Makerfabs/MaTouch-ESP32-S3-7.5-Eink-AI-Mic-Array/image/001.bmp

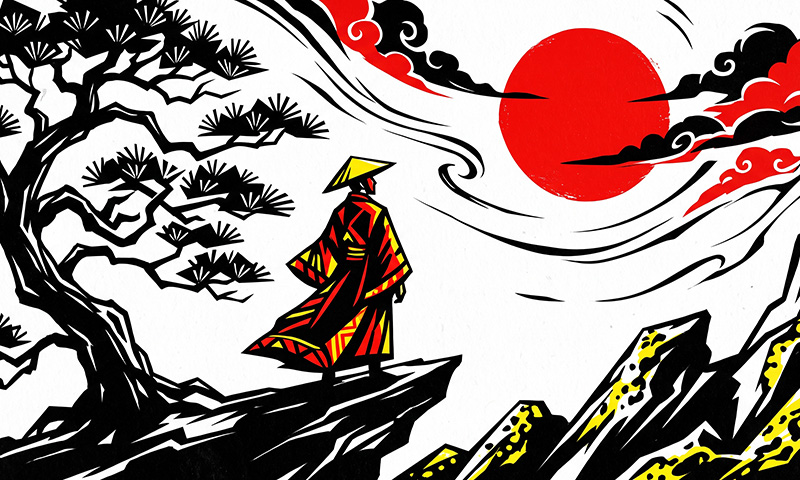
image/001.bmp
