Makerfabs/MaTouch-ESP32-S3-7.5-Eink-AI-Mic-Array/image/002.bmp

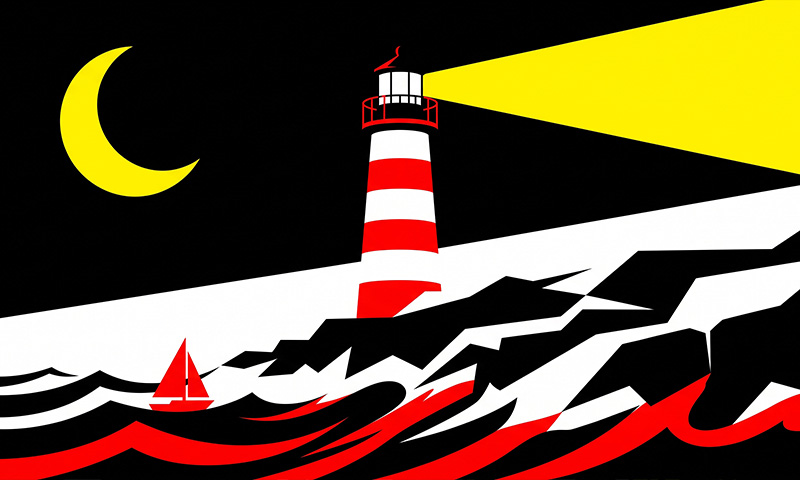
image/002.bmp
