Makerfabs/MaTouch-ESP32-S3-7.5-Eink-AI-Mic-Array/image/003.bmp

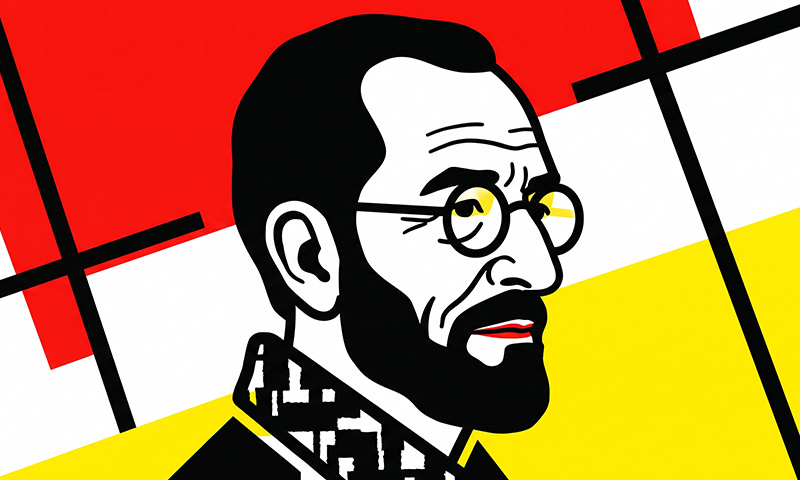
image/003.bmp
